DavidRodrii/wes237a-final-project/AWS EC2/Node-RED/Node-RED-Flow.png

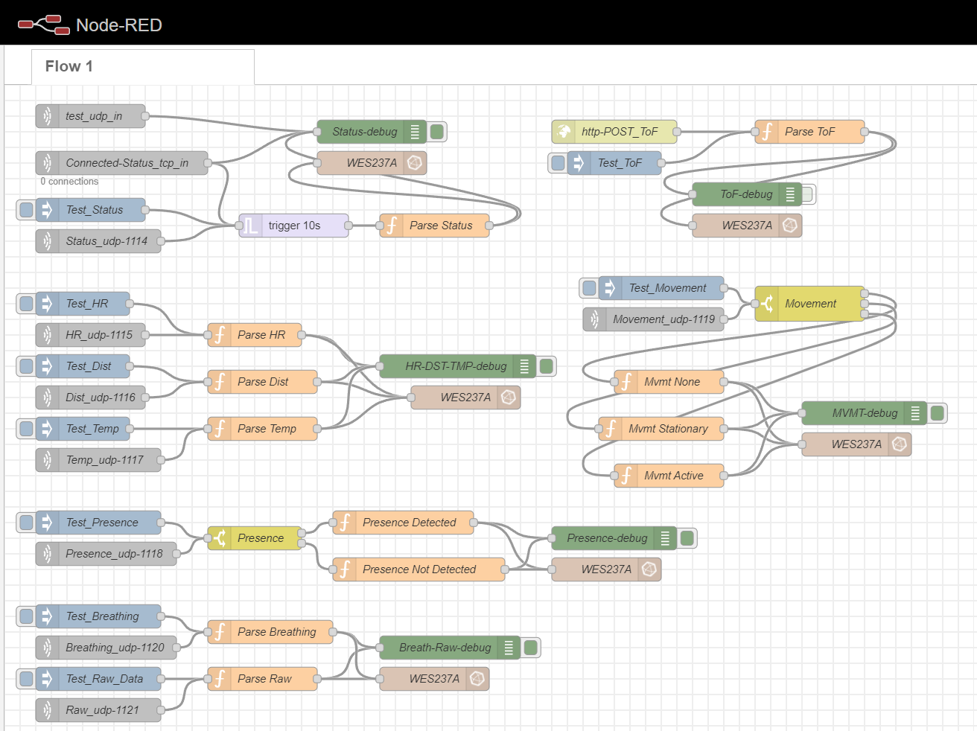
AWS EC2/Node-RED/Node-RED-Flow.png
