DavidRodrii/wes237a-final-project/Docs/Images/3D Renders/Full-Assem_v1-PYNQ_Z2_MiniTripod_Render-3.png

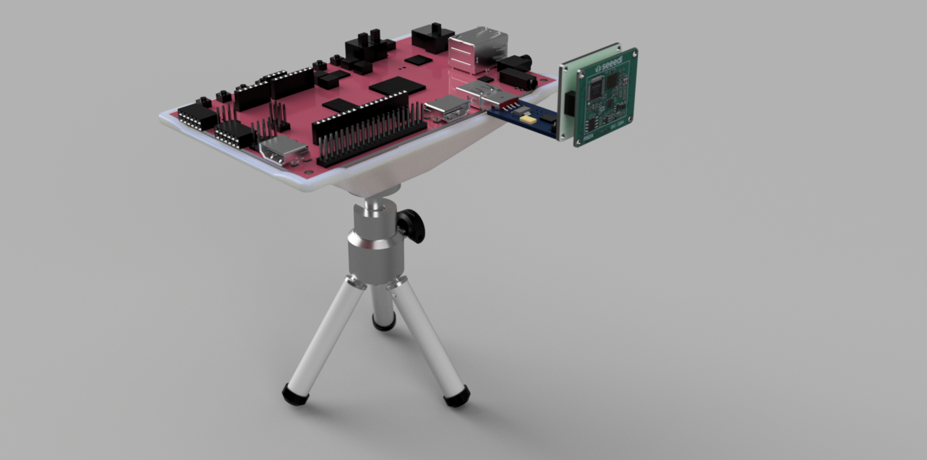
Docs/Images/3D Renders/Full-Assem_v1-PYNQ_Z2_MiniTripod_Render-3.png
