DavidRodrii/wes237a-final-project/Docs/Images/wes237a-final-project_main-process_Flow.png

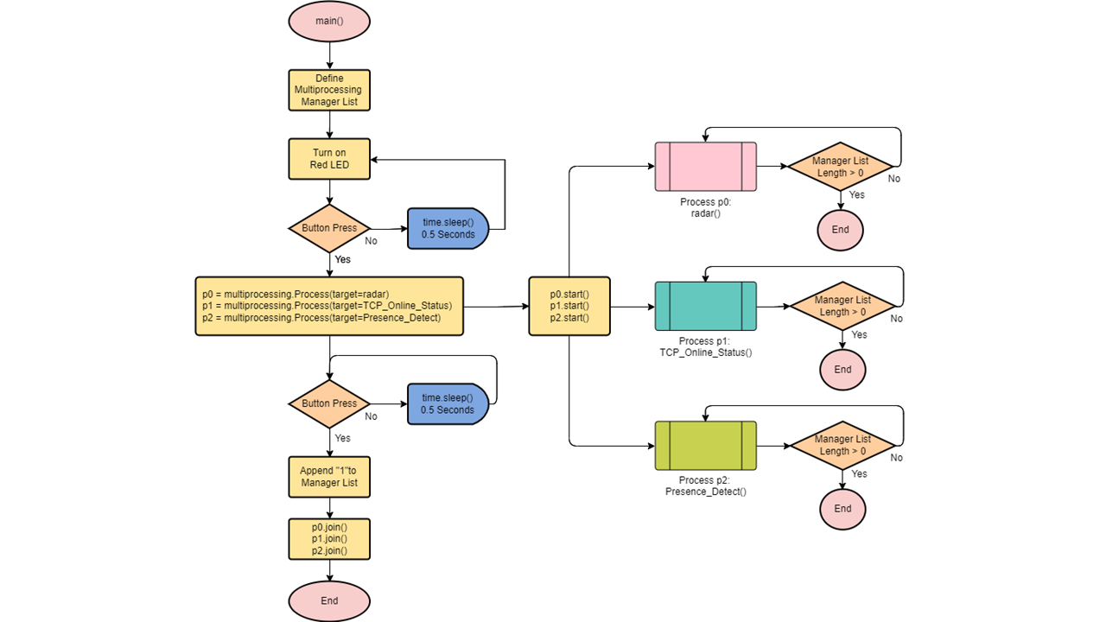
Docs/Images/wes237a-final-project_main-process_Flow.png
