DavidRodrii/wes237a-final-project/Docs/Images/wes237a-final-project_radar-process_Flow.png

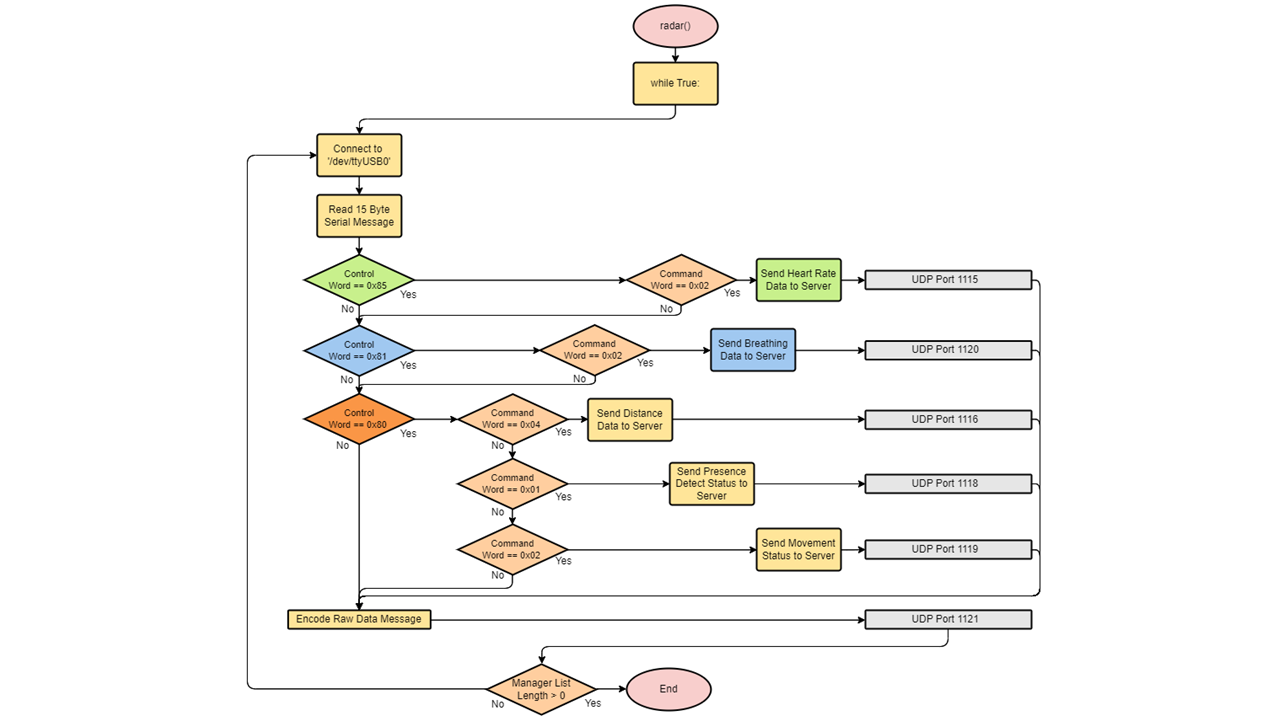
Docs/Images/wes237a-final-project_radar-process_Flow.png
