DavidRodrii/wes237a-final-project/Docs/Images/Final-Project-Assembled/iso-med.jpg

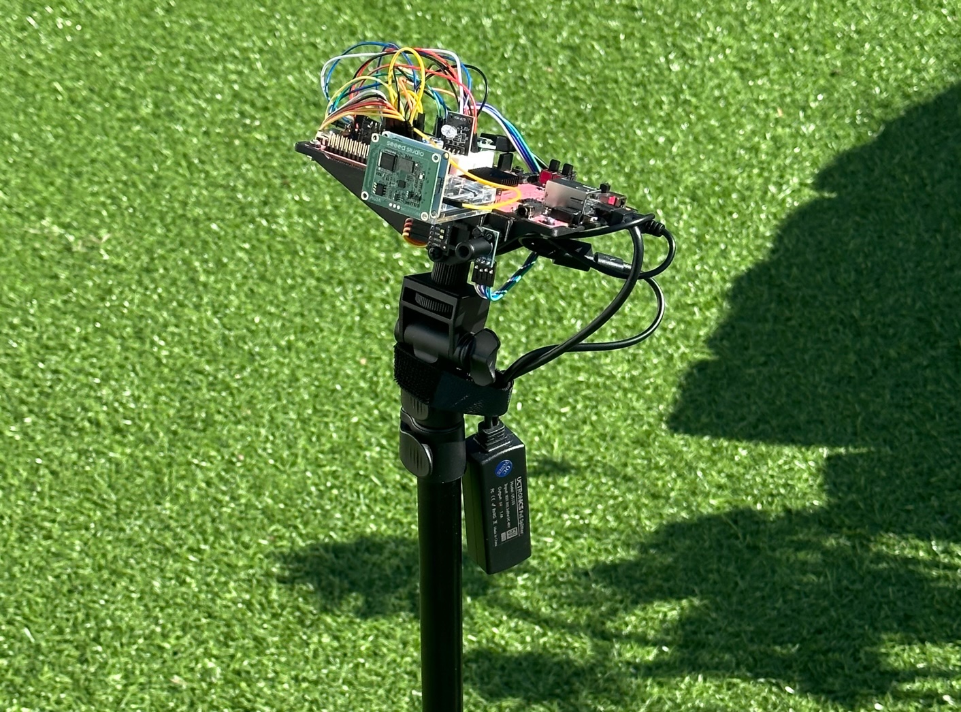
Docs/Images/Final-Project-Assembled/iso-med.jpg
