DavidRodrii/wes237a-final-project/Docs/Images/Final-Project-Assembled/iso-port.jpg

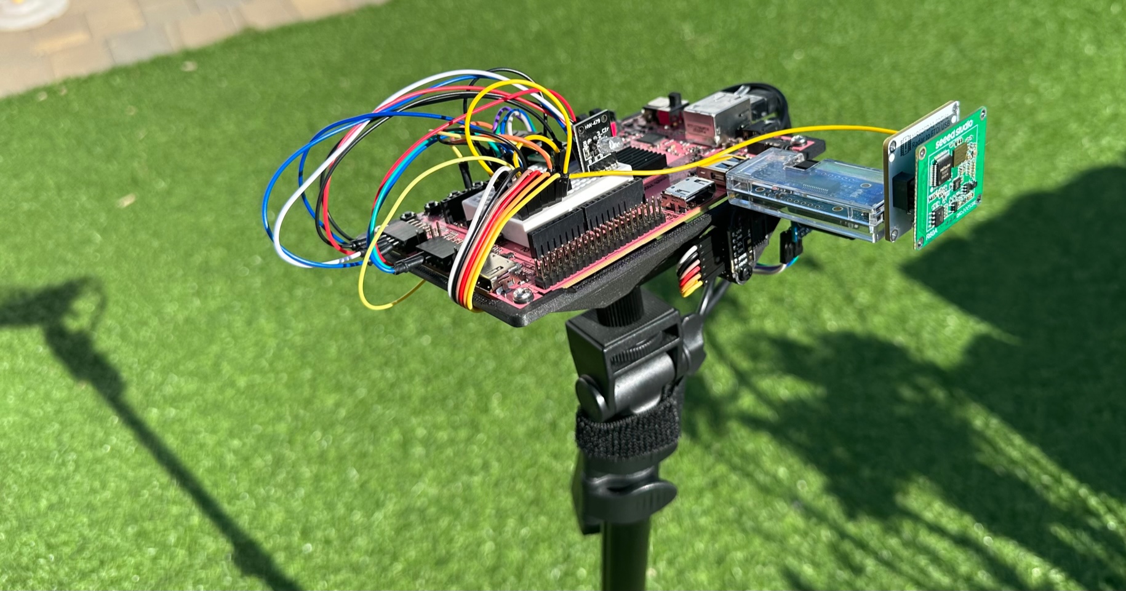
Docs/Images/Final-Project-Assembled/iso-port.jpg
